freeDSP/freeDSP-CLASSIC-SMD-BALANCED/DOCUMENTATION/PICTURES/DSC_0359.JPG

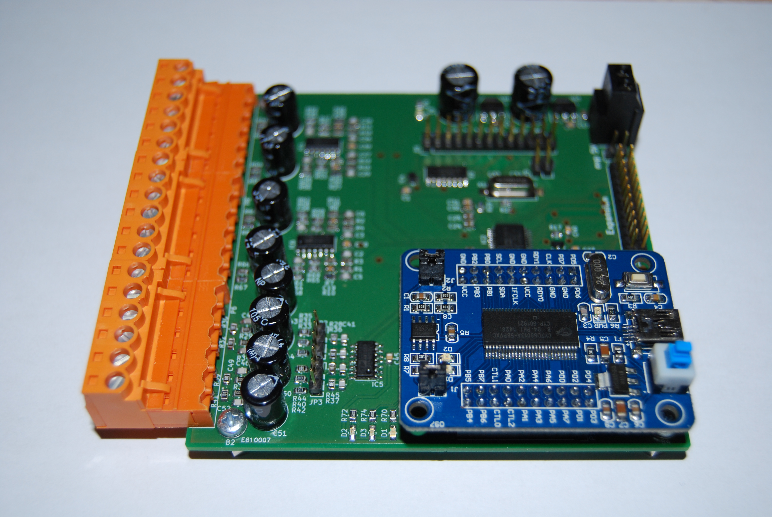
DOCUMENTATION/PICTURES/DSC_0359.JPG
